maxwass/upenn_quadrotor_share/controller/src/sonar.cpp

#include "sonar.h"
//g++ sonar.cpp logger.cpp -I ../include -std=c++11

Sonar::Sonar(std::string PATH2SONAR, int minDist, int maxDist)
{

	(this->minDist) = minDist;
	(this->maxDist) = maxDist;

	distController_.setGains(0.05, 0.1, 0.1);
	distController_.setDesiredValue(1.00);

	//(this->data_size) = DATASIZE; //including first and last checkbytes
	open_port(PATH2SONAR, 1);
	printf("END SONAR \n");
}
int Sonar::open_port(std::string PATH2SONAR, int bytes_to_block)
{
	printf("Opening an sonar USB port...   ");
	struct termios newtio;
	int port;
	port = open(PATH2SONAR.c_str(), O_RDWR | O_NOCTTY);

	tcgetattr(port, &newtio);
	cfsetospeed(&newtio, BAUDRATE_SONAR);
	cfsetispeed(&newtio, BAUDRATE_SONAR);

	//set the number of data bits.
	newtio.c_cflag &= ~CSIZE;  // Mask the character size bits
	newtio.c_cflag |= CS8;

	//set the number of stop bits to 1
	newtio.c_cflag &= ~CSTOPB;

	//Set parity to None
	newtio.c_cflag &=~PARENB;

	//set for non-canonical (raw processing, no echo, etc.)
	newtio.c_iflag = IGNPAR; // ignore parity check close_port
	newtio.c_oflag = 0; // raw output
	newtio.c_lflag = 0; // raw input

	//Time-Outs -- won't work with NDELAY option in the call to open
	newtio.c_cc[VMIN]  = bytes_to_block;   // block reading until RX x characers. If x = 0, it is non-blocking.
	newtio.c_cc[VTIME] = 0;   // Inter-Character Timer -- i.e. timeout= x*.1 s

	//Set local mode and enable the receiver
	newtio.c_cflag |= (CLOCAL | CREAD);

	//tcflush(port, TCIFLUSH);
	//Set the new options for the port...
	int status=tcsetattr(port, TCSANOW, &newtio);
	if (status != 0) 
	{
		printf("Configuring SONAR comport failed\n");
		
	}
	
	(this->port) = port;
	(this->PATH2SONAR) = PATH2SONAR;
	clean();

	if (port < 0) 
	{
		printf("\n Error opening USB port: %i !!", port);
		//open_port("/dev/ttyUSB1", 1);
        }
	 else   printf("Done!\n");
	printf("Port Name: %i \n", port);

	return port;
}
int Sonar::get_sonar_data(SonarTest& s)
{
//the sensor outputs 6 bytes at a time. The first byte is 82 in decimal, the next 4 bytes are the the constituent parts of a 32 bit int form Most Significant Byte to Least Significant Byte, the 6th byte is 13 in decimal combine four unsigned chars into one 32 bit int
	
//select: clear read_ds(set of file_descriptors to watch for reading), add port to this set, set time to 0 to returnimmediately,
    // select returns the number of fd's ready
    FD_ZERO(&read_fds);
    FD_SET(port, &read_fds);
    no_timeout.tv_sec  = 0;
    no_timeout.tv_usec = 0;

    if(first_call)
    {
	first_call = false;
	timer.update();
    }

    int toReturn = check_first_read_test(s);

    if( (this->timeSinceLastRead()) > (this->sonarTimeout) ) (this->sonarStatus) = false;
    else 						     (this->sonarStatus) = true;

    if( (toReturn>0) && sonarStatus)
    {
	distController_.update(toReturn, timer.getDt());

    }

    return toReturn;

}

SonarTest Sonar::get_stats(void)
{
	SonarTest s = {0};
	//printf("Not Ready to Read Count:  %ld, Ready to Read Count: %ld \n\n",  (this->num_fds_0), (this->num_fds_1));

	s.dt   		 = timer.getDt();;
	s.index 	 = this->index;
	s.distance       = this->returnLastDistance();
	s.foundFirstByte = this->foundFirstByte;
	s.num_fds_n1	 = this->num_fds_n1;
	s.num_fds_0	 = this->num_fds_0;
	s.num_fds_1	 = this->num_fds_1;
	s.num_fds_p	 = this->num_fds_p;
	s.lastByte	 = this->lastByte;
	return s;
}
int Sonar::check_first_read_test(SonarTest& s)
{
//Once we find start byte, we begin filling in array byte-by-byte until we get 4 bytes. We then confirm that the next byte is the last byte, if it is we then cast the array into a 32 bit integer and return. If the last byte is incorrect, we dicard array, reset index, and continue searching for start byte again.
    int num_fds = select(port+1, &read_fds, NULL, NULL, &no_timeout); 
   	int returnVal= -10;
   s.num_fds = num_fds;
   if(num_fds == -1)      (this->num_fds_n1)++;
   else if (num_fds == 0) (this->num_fds_0)++;
   else if (num_fds == 1) (this->num_fds_1)++; 
   else if (num_fds > 1)  (this->num_fds_p)++;
  //No data ready to read
    if(num_fds == 0)  
    {
	s.succ_read = -1;
	returnVal= -1;
	return -1;
    }
    //select returned an error
    else if(num_fds ==-1)
    {
	s.succ_read=  -2;
	returnVal= -2;

	return -2;
    }

    //A file descriptor is ready to read: check which one
    //else if(FD_ISSET((this->port) , &read_fds))
      else if(num_fds ==1)   
	{
                char sensor_byte[1] = {255}; 

                lseek(port, -(this->data_size), SEEK_END);
		
     		int result = read(port, &sensor_byte[0], 1);
		char a = sensor_byte[0];
		(this->lastByte) = a;
				if(result == 0) 
		{
			//printf("sonar: read 0 bytes \n");
			clean();
			returnVal = -3;
		}
		//finished, found all bytes
		else if( (foundFirstByte == true) && (index == 4) )
		{
			//printf("		number of bytes read: %i, index: %i, byte: %d \n", result, index, a);


			if(sensor_byte[0] == 13) 
			{	
				uint32_t range_char = 0;
				sscanf(&dist[0], "%d", &range_char);
				//printf("read last byte 13 with index = 4 \n");
				//printf("					Distance: %i \n", range_char);
				clean();
				timer.update();
				(this->last_distance) = range_char;
				returnVal = range_char;
		
			}
			else
			{
				//printf("read last byte NOT 13 with index = 4\n");
				tcflush(port, TCIFLUSH);
				clean();
				returnVal = -4;
			}		
		}
		
		//still collecting bytes, add to array, increment index 
		else if(foundFirstByte == true)
		{
			//printf("		adding to array & index++\n");
			dist[index] = sensor_byte[0];
			index++;
			returnVal = -5; 
		}
		//havent found first or last byte, check each byte to see if this is first
		else if(sensor_byte[0] == 82)
		{
			//printf("found first byte\n");
			foundFirstByte = true;
			index = 0;
			returnVal = -6;
		}
		else 
		{
			returnVal = -7;
			clean();
		}

		s.succ_read = returnVal;
		s.lastByte = sensor_byte[0];
		s.distance = returnVal;
		s.index = index;
		s.foundFirstByte = foundFirstByte;
		s.foundLastByte  = foundLastByte;

		
		
		return returnVal;
	}
		clean();
	
		return -8;
}
void Sonar::clean(void)
{
	index = 0;

	foundFirstByte = false;
	foundLastByte = false;
}
void Sonar::print_raw_bytes(const char arr[], int arr_length)
{
        printf("\nBytes: \n");
        for(int i = 0; i < arr_length; i++) 
	{
		printf("%i : %d ,", i, arr[i]); //NOTE: PRINTING HEX REPRES OF CHAR, NEED TO PRINT DECIMAL
        	//if(arr[i] == 82) printf("FOUND 82 in %i th position \n",i);
	}
	printf("Location of first byte: %i", indexOfStartByte(arr, arr_length));

	printf("\n\n\n");
}
float Sonar::timeSinceLastRead(void)
{
		return timer.getDt();
}
int Sonar::indexOfStartByte(const char arr[], int arr_length)
{
		//iterate through array and find which index, starting at zero is the first (82)
		int i;
		for(int i = 0; i < arr_length; i++)	if(arr[i] == 82) return i;
		return -1;
}
float Sonar::getDt(void)
{
	return timer.getDt();
}
int Sonar::returnLastDistance(void)
{
	if(this->sonarStatus)   return (this->last_distance);
	else 		  	return maxDist;
}
void Sonar::printStats(void)
{
 
	//printf("Not Ready to Read Count:  %ld, Ready to Read Count: %ld \n\n",  (this->num_fds_0), (this->num_fds_1));
	printf("last_distance: %i, freq: %f \n\n", last_distance, 1/timer.getDt());
	distController_.printData();
}
int Sonar::getStatus(void)
{
	return this->sonarStatus;
}
void Sonar::distanceControlOn(float dist)
{
	distController_.autoControlOn(dist);
}
void Sonar::distanceControlOff(void)
{
	distController_.autoControlOff();
}
bool Sonar::isDistControlOn(void)
{
	return distController_.isAutoControlOn();
}
void Sonar::getErrors(Errors& e)
{
	e.desired_value = distController_.getDesiredValue();
	e.prop		= distController_.getPropError();
	e.deriv         = distController_.getDerivError();
	e.integral	= distController_.getIntegralError();

}

float Sonar::getPropError()
{
	return distController_.getPropError();
}

float Sonar::getDerivError()
{
	return distController_.getDerivError();
}

float Sonar::getIntegralError()
{
        return distController_.getIntegralError();
}


float Sonar::getDesiredDistance(void)
{
	return distController_.getDesiredValue();
}
float Sonar::getControlOutput(void)
{
	return distController_.getControlOutput();
}
/*
int main()
{
	int minDist = 500;
	int maxDist = 1500;
	Sonar sonar_x_pos("/dev/ttyUSB1", minDist, maxDist);

	//logger logger("file.log", 100, true);
	
	while(1)
	{

	SonarTest s = {0};
	int dist_mm = sonar_x_pos.get_sonar_data(s);
	
	if(dist_mm >0) sonar_x_pos.printStats();
	if(dist_mm == 300) sonar_x_pos.distanceControlOn(350);

	//printf("distance (mm): %i, freq: %f, index: %i, distance: %i, foundFirstByte: %i, byte_read: %d \n", sonar_x_pos.returnLastDistance(), 1/sonar_x_pos.getDt(), sonar_x_pos.index, sonar_x_pos.distance, sonar_x_pos.foundFirstByte, sonar_x_pos.lastByte);

	}

	

}
*/
