maxwass/upenn_quadrotor_share/controller/src/joystick_send.cpp

//CODE USED TO SEND JOYSTICK DATA

/*
  2  * Hidraw Userspace Example
  3  *
  4  * Copyright (c) 2010 Alan Ott <alan@signal11.us>
  5  * Copyright (c) 2010 Signal 11 Software
  6  *
  7  * The code may be used by anyone for any purpose,
  8  * and can serve as a starting point for developing
  9  * applications using hidraw.
 10  */
 #include <linux/types.h>
 #include <linux/input.h>
 #include <linux/hidraw.h>
 #include <sys/ioctl.h>
 #include <sys/types.h>
 #include <sys/stat.h>
 #include <fcntl.h>
 #include <unistd.h>
 #include <termios.h>
 #include <stdio.h>
 #include <string.h>
 #include <stdlib.h>
 #include <errno.h>
 #include <sys/time.h>
 #include "joystick_send.h"
 #include "Xbee.h"
  /*
 18  * Ugly hack to work around failing compilation on systems that don't
 19  * yet populate new version of hidraw.h to userspace.
 20  */
 #ifndef HIDIOCSFEATURE
 #warning Please have your distro update the userspace kernel headers
 #define HIDIOCSFEATURE(len)    _IOC(_IOC_WRITE|_IOC_READ, 'H', 0x06, len)
 #define HIDIOCGFEATURE(len)    _IOC(_IOC_WRITE|_IOC_READ, 'H', 0x07, len)
 #endif
 struct timeval t_init, t_now;
 double t, del_t, del_t_;
 double t_prev = 0.0;
double t_prev_ = 0.0;
 const char *bus_str(int bus);
 
 int saturation_value(float input, float ceiling, float floor)
 {
 	if (input > ceiling) input = ceiling;
 	if (input < floor) input = floor;
 	
 	return input;

 }
 
 
 int main(int argc, char **argv)
 {
 	 float send_buf[5];
 	 double t_temp = 13000;
 	 gettimeofday(&t_init,NULL);
 	 
 	 int thrust_h = 53;
 	 int thrust_l = -52;
 	 
 	 int roll_h = 48; //left end
 	 int roll_l = -41; //right end
 	 
 	 int pitch_h = 52;
 	 int pitch_l = -55;
 	 
 	 int yaw_h = 46; //left end
 	 int yaw_l = -42; //right end
 	 
 	 
 	 printf("Opening an USB port...   ");//Opens the usb Port
	int usb0 = open_port();
	if (usb0 <0)
        	printf("\n Error opening an USB0 port!!\n");
        else
        	printf("Done!\n");
        usleep(14000);
 	
         int fd;
         int i, res, desc_size = 0;
         char buf[8];
         struct hidraw_report_descriptor rpt_desc;
         struct hidraw_devinfo info;
         char *device = "/dev/hidraw1";
 
         if (argc > 1)
                 device = argv[1];
 
         /* Open the Device with non-blocking reads. In real life,
            don't use a hard coded path; use libudev instead. */
         fd = open(device, O_RDWR|O_NONBLOCK);
 
         if (fd < 0) {
                 perror("Unable to open device");
                 return 1;
         }
 
         memset(&rpt_desc, 0x0, sizeof(rpt_desc));
         memset(&info, 0x0, sizeof(info));
         memset(buf, 0x0, sizeof(buf));
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
